SpykieLucilius/RootNet-SmartPot/kicad/Kicad_RootNet/Kicad_RootNet.kicad_sch

## KiCad design kicad/Kicad_RootNet/Kicad_RootNet.kicad_sch (2026-05-06)

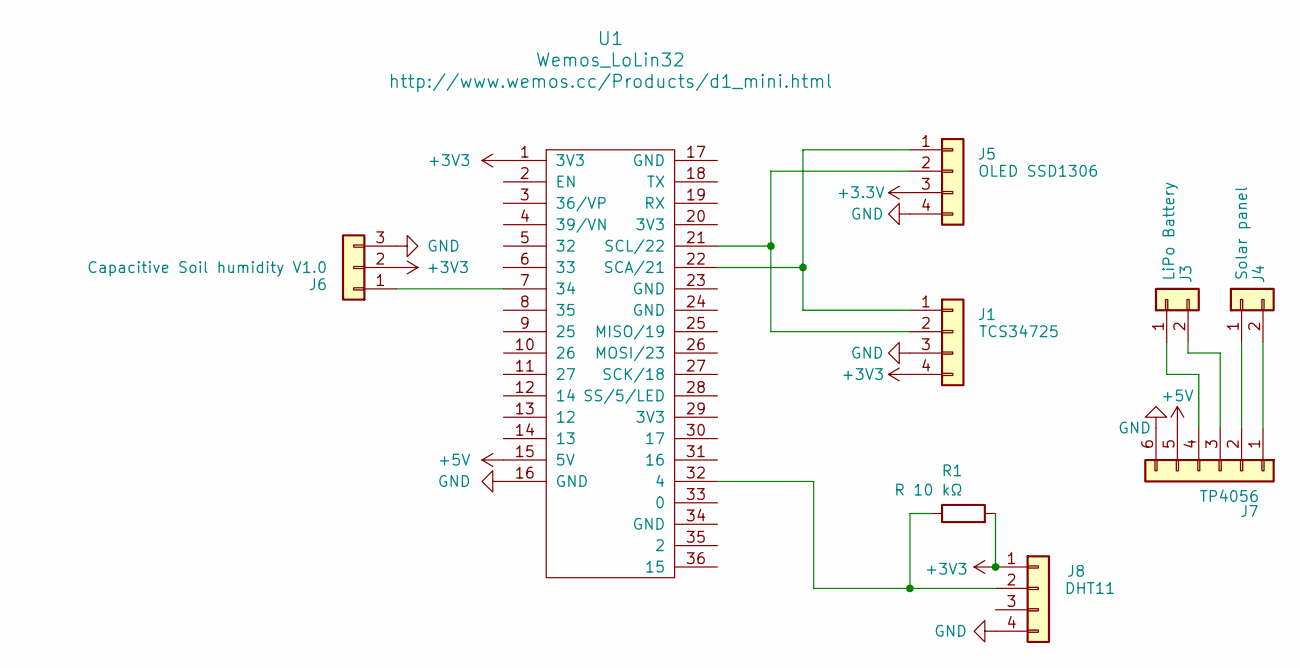
[picture p2: schematic Kicad_RootNet.kicad_sch]

Parts:
J1: TCS34725
J3: LiPo Battery
J4: Solar panel
J5: OLED SSD1306
J6: Capacitive Soil humidity V1.0
J7: TP4056
J8: DHT11
R1: R 10 kΩ
U1: Wemos_LoLin32

Connections:
+3.3V: J5.3
+3V3: J1.4, J6.2, J8.1, R1.2, U1.1 (3V3)
+5V: J7.5, U1.15 (5V)
GND: J1.3, J5.4, J6.3, J7.6, J8.4, U1.16 (GND)
unnamed: J1.1, J5.1, U1.22 (SCA/21)
unnamed: J1.2, J5.2, U1.21 (SCL/22)
unnamed: J3.1, J7.4
unnamed: J3.2, J7.3
unnamed: J4.1, J7.2
unnamed: J4.2, J7.1
unnamed: J6.1, U1.7 (34)
unnamed: J8.2, R1.1, U1.32 (4)
